bbkbarbar/IoT-thermostat_Project/NodeMcu_IoT_Climate_Thermostat_DHT11_with_SerialOut_with_MQTT/common_methods.h

String getHTMLAutomaticGoBack(short millis){
	String htmlPart = "<script language=\"JavaScript\" type=\"text/javascript\">\n";
    htmlPart += "setTimeout(\"window.history.go(-1)\"," + String(millis) + ");\n";
    htmlPart += "</script>\n";
	return htmlPart;
}
